1cfer/Tars/docs/IMG_0967.jpg

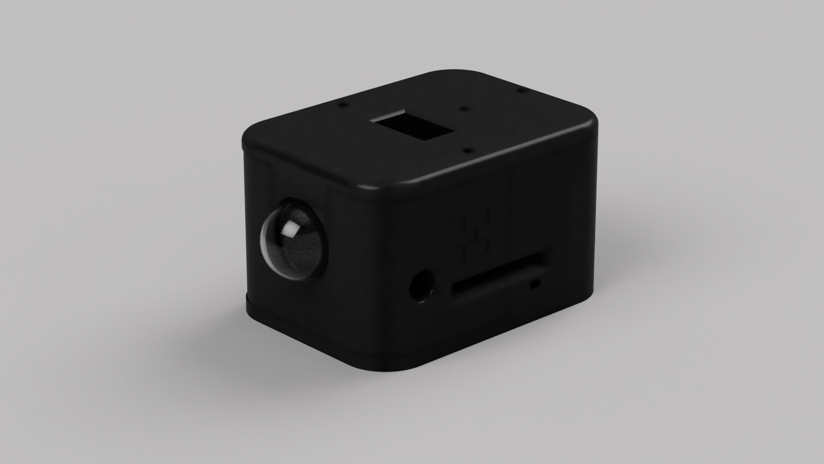
docs/IMG_0967.jpg
