1cfer/Tars/firmware/TARS/DisplayManager.h

#ifndef DISPLAYMANAGER_H
#define DISPLAYMANAGER_H
#include <Arduino.h>

void drawAllSensors();
void updateDisplay();
void displayStateInfo(const char* estado);
void displayDeveloperInfo();

// Nuevas funciones para el menú de WiFi interactivo
void displayWiFiList(int selected, int offset, int total);
void displayAPAlert();

#endif
